AntoninPvr/PS23023/5v_supply/5v_supply.kicad_pcb

## KiCad design kicad/guitarpedalv2/guitarpedalv2.kicad_sch

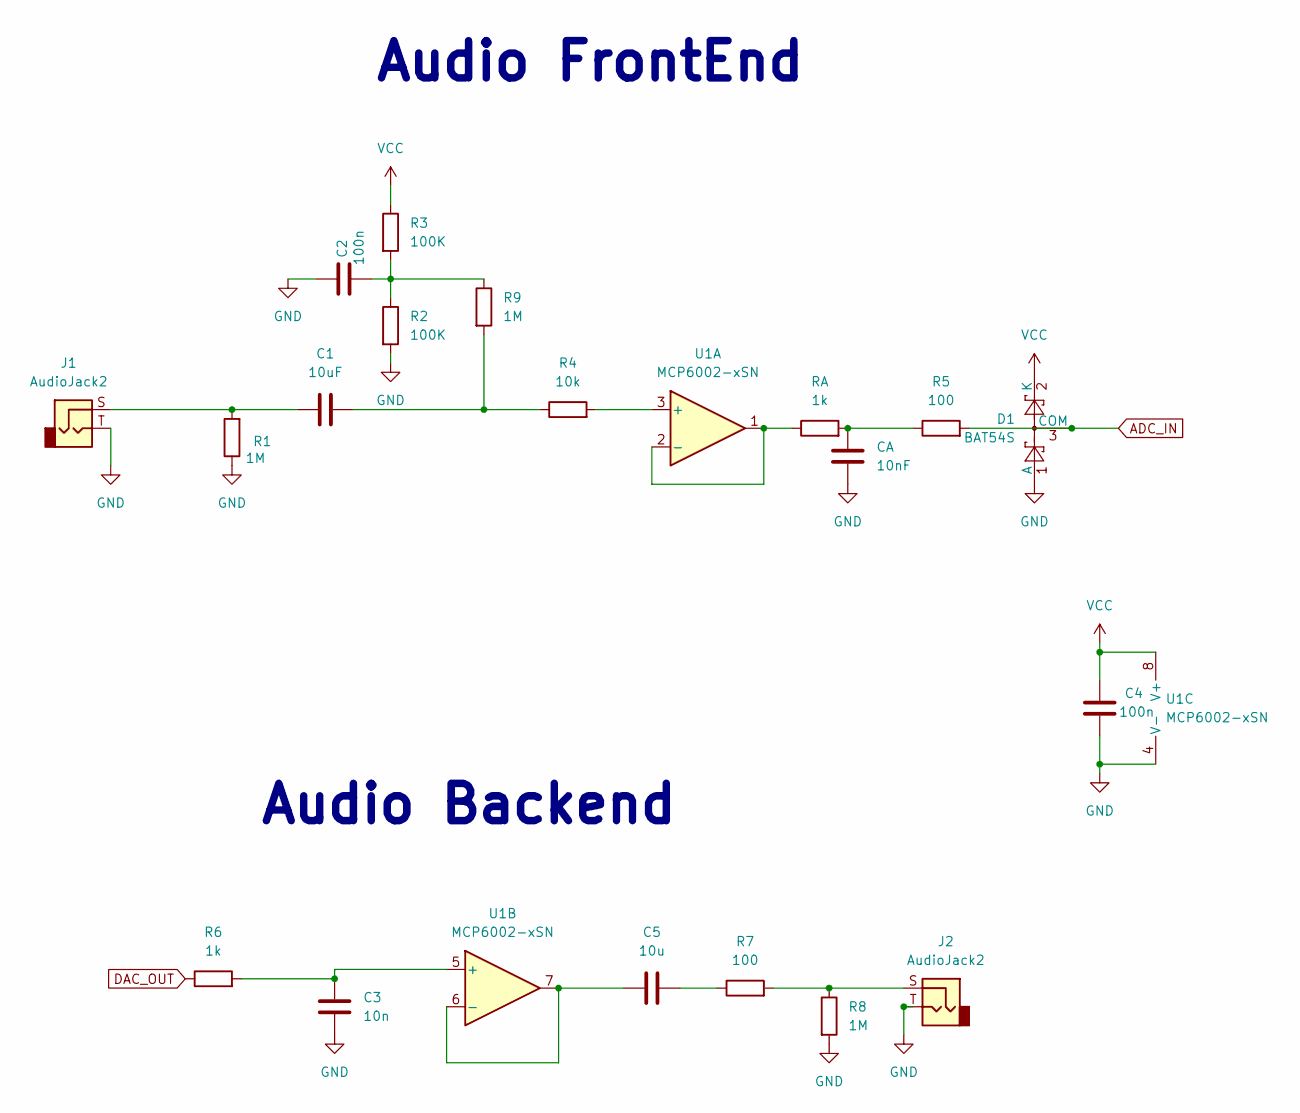
[picture p10: schematic guitarpedalv2.kicad_sch]

Parts:
C1: 10uF
C2, C4: 100n
C3: 10n
C5: 10u
CA: 10nF
D1: BAT54S; SOT-23
J1, J2: AudioJack2
R1, R8, R9: 1M
R2, R3: 100K
R4: 10k
R5, R7: 100
R6: 1k
RA: 1k
U1: MCP6002-xSN

Connections:
ADC_IN: D1.3 (COM), R5.2
DAC_OUT: R6.1
GND: C2.2, C3.2, C4.2, CA.2, D1.1 (A), J1.T, J2.T, R1.1, R2.2, R8.2, U1.4 (V-)
unnamed: C1.1, J1.S, R1.2
unnamed: C1.2, R4.1, R9.2
unnamed: C2.1, R2.1, R3.2, R9.1
unnamed: C3.1, R6.2, U1.5 (+)
unnamed: C5.1, R7.1
unnamed: C5.2, U1.6 (-), U1.7
unnamed: CA.1, R5.1, RA.2
unnamed: J2.S, R7.2, R8.1
unnamed: R4.2, U1.3 (+)
unnamed: RA.1, U1.1, U1.2 (-)
VCC: C4.1, D1.2 (K), R3.1, U1.8 (V+)

Notes on the sheet:
Audio FrontEnd
Audio Backend
